choonway/ChIPs/ChIPs_FreeCAD/chip_25mm_2.FCStd

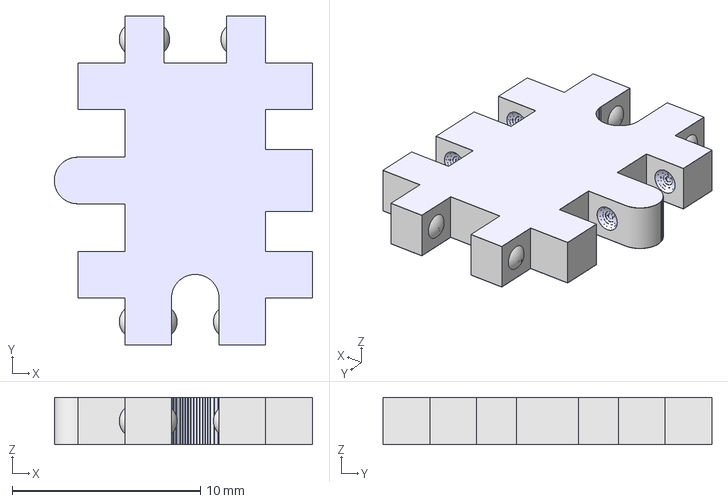
[picture p43: CAD file, 2022-09-11]
ChIPs_FreeCAD/chip_25mm_2.FCStd
13.7 x 17.5 x 2.50 mm
solid (Meshed)
