choonway/ChIPs/ChIPs_25/chip_25mm_5.stl

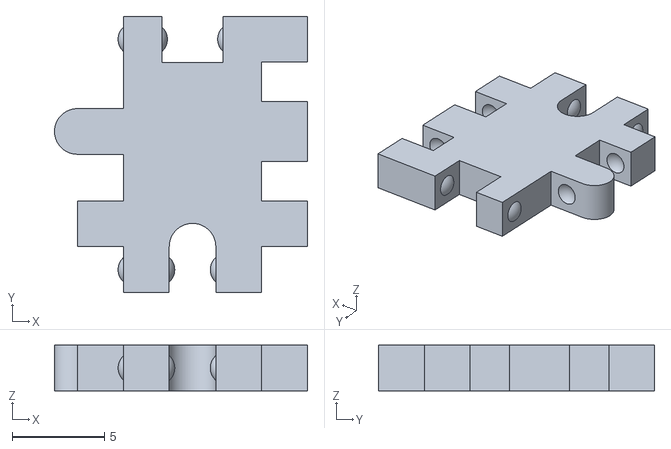
[picture p44: CAD file, 2022-09-11]
ChIPs_25/chip_25mm_5.stl
13.7 x 15.0 x 2.47
