choonway/ChIPs/ChIPs_37.5/ChIPs_3x36.3mf

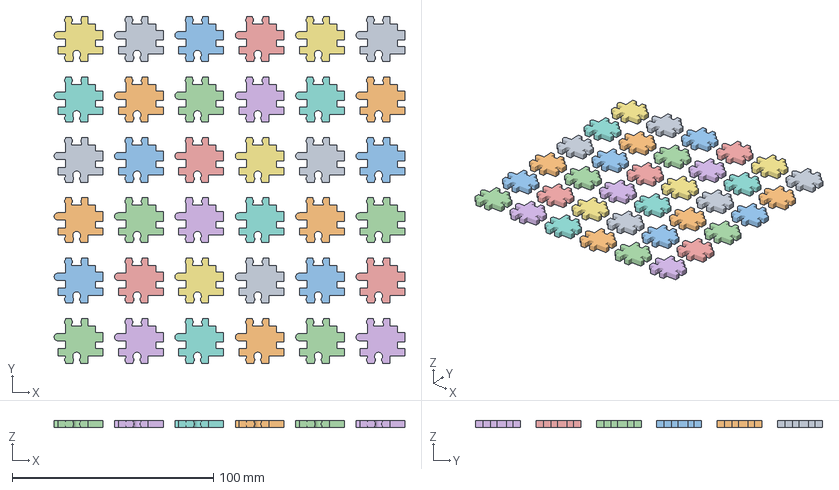
[picture p45: CAD file, 2022-05-08]
ChIPs_37.5/ChIPs_3x36.3mf
174.3 x 172.4 x 3.65 mm
