choonway/ChIPs/ChIPs_37.5/ChIPs_1.stl

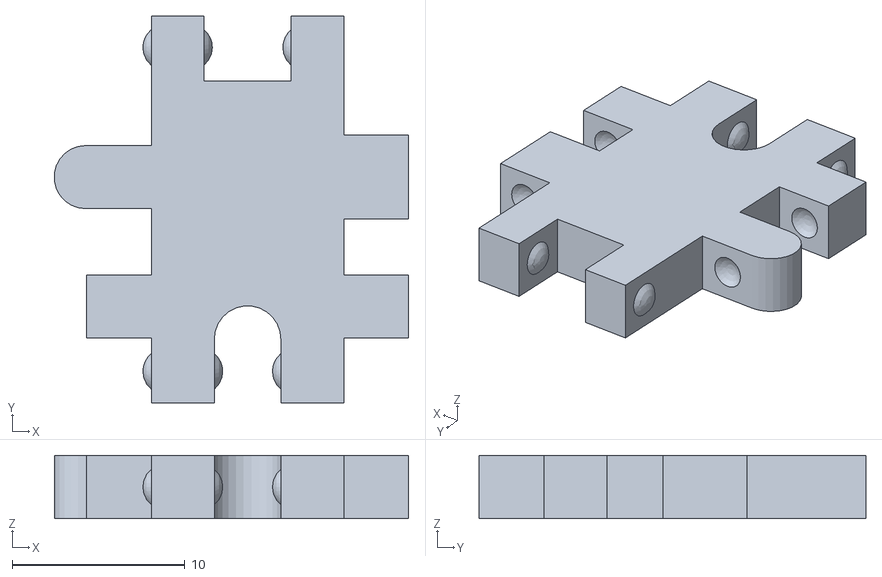
[picture p47: CAD file, 2022-05-08]
ChIPs_37.5/ChIPs_1.stl
20.5 x 22.4 x 3.65
