choonway/ChIPs/ChIPs_25/chip_25mm_2.stl

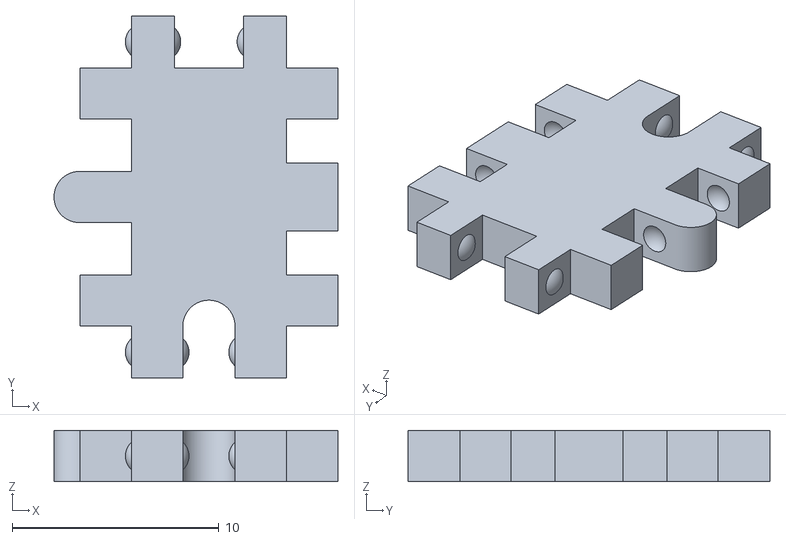
[picture p48: CAD file, 2022-09-11]
ChIPs_25/chip_25mm_2.stl
13.7 x 17.5 x 2.47
