choonway/ChIPs/ChIPs_37.5/ChIPs_2.stl

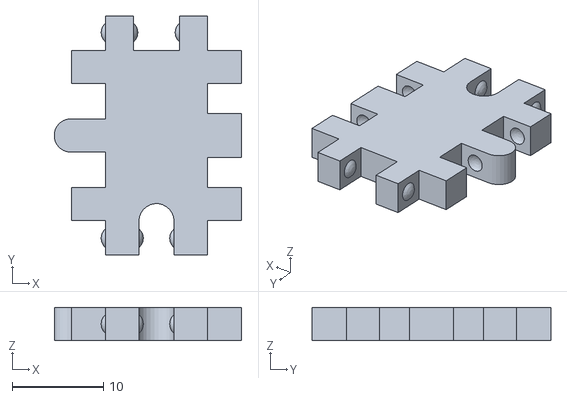
[picture p49: CAD file, 2022-05-08]
ChIPs_37.5/ChIPs_2.stl
20.5 x 26.2 x 3.65
