choonway/ChIPs/ChIPs_25/chip_25mm_4.stl

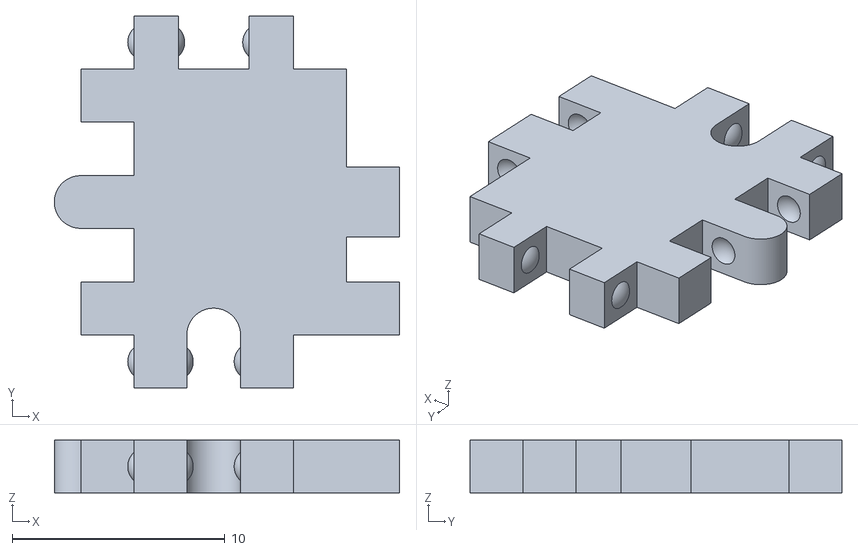
[picture p50: CAD file, 2022-09-11]
ChIPs_25/chip_25mm_4.stl
16.2 x 17.5 x 2.47
